HZH6661314/LC-Power-Supply/code/LC_Power/Docs/嵌入式架构设计培训计划（基于100W数字电源项目）.md

# 嵌入式架构设计培训计划（基于100W数字电源项目）

## 培训背景

**学员水平：** 初级（1-2年经验）
**培训目标：** 掌握工程级别的嵌入式架构设计能力
**培训方式：** 理论与实战结合
**实战项目：** 100W数控便携可调直流电源（STM32F334 + Buck-Boost）

------

## 项目架构概览

根据《数控电源代码规范.md》，项目采用**六层架构**：

```
┌─────────────────────────────────────────────────────┐
│  0_SysCore (Scheduler层)                            │
│  - SysTick时间片轮询                                │
│  - 全局中断配置                                      │
│  - 临界区并发保护                                    │
└─────────────────────────────────────────────────────┘
                        ↓ 可调用下方各层
┌─────────────────────────────────────────────────────┐
│  1_Product层                                        │
│  - UI显示、上位机协议、参数存储调度                  │
└─────────────────────────────────────────────────────┘
                        ↓
┌─────────────────────────────────────────────────────┐
│  2_Application层                                    │
│  - 状态机(BOOT/STANDBY/SOFTSTART/RUNNING/FAULT)    │
│  - 保护逻辑、PD诱骗握手                             │
└─────────────────────────────────────────────────────┘
                        ↓
┌─────────────────────────────────────────────────────┐
│  3_Control层 【纯C数学运算，严禁依赖底层】           │
│  - 电压环PID、电流环2P2Z、软件滤波器                 │
└─────────────────────────────────────────────────────┘
                        ↓
┌─────────────────────────────────────────────────────┐
│  4_Driver层                                         │
│  - W25Q256驱动、OLED驱动、INA240参数换算            │
└─────────────────────────────────────────────────────┘
                        ↓
┌─────────────────────────────────────────────────────┐
│  5_BSP层                                            │
│  - STM32F334 HAL库、HRTIM、ADC/DMA、SPI底层收发     │
└─────────────────────────────────────────────────────┘
```

------

## 第一阶段：架构设计三大铁律（2周，理论为主）

### 模块1：铁律一 - 严格的单向依赖与隔离

**核心原则：**

1. **上层可以调用下层，下层绝对不能知道上层的存在**
2. **同层之间禁止直接通信，必须通过全局Context**

**理论讲解：**

**为什么需要单向依赖？**

- 防止循环依赖（A调B，B调A，代码改不动）
- 保证可移植性（底层换芯片，上层不受影响）
- 降低耦合度（修改一个模块不影响其他模块）

**正确示例：**

```c
// ✅ 允许：Product层读取Control层数据
void UI_Display_Voltage(void) {
    int32_t voltage = g_sys_context.real_voltage_mv;
    TFT_DrawNumber(voltage);
}
```

**错误示例：**

```c
// ❌ 严禁：Driver层ADC中断直接调用Application层
void ADC_IRQHandler(void) {
    uint32_t adc_value = ADC1->DR;
    App_State_SwitchTo(STATE_FAULT);  // 错误！底层不能调上层
}
```

**正确做法：**

```c
// ✅ ADC中断只处理数据
void ADC_IRQHandler(void) {
    g_sys_context.adc_raw_value = ADC1->DR;
}

// Application层在1ms任务中检查
void Task_1ms(void) {
    if (g_sys_context.adc_raw_value > OVP_THRESHOLD) {
        App_State_SwitchTo(STATE_FAULT);
    }
}
```

**同层通信规则：**

```c
// ❌ 错误：protection.c直接调用ui.c
void Protection_Check(void) {
    if (over_voltage) {
        UI_ShowFaultDialog();  // 错误！同层直接调用
    }
}

// ✅ 正确：通过全局Context通信
void Protection_Check(void) {
    if (over_voltage) {
        g_sys_context.fault_code = FAULT_OVP;
    }
}

void UI_Task_50ms(void) {
    if (g_sys_context.fault_code != FAULT_NONE) {
        UI_ShowFaultDialog();
    }
}
```

**实战练习：**

1. 绘制你项目的依赖关系图
2. 检查代码中是否有违反单向依赖的地方
3. 设计全局Context结构体（PowerSystemContext_t）
4. 重构一个模块，消除跨层调用

------

### 模块2：铁律二 - 平台移植测试（试金石）

**核心原则：** 假设明天STM32F334缺货，必须换用TI C2000 DSP。

- **合格线：** 只需要删掉并重写`4_Driver`和`5_BSP`文件夹
- **黄金标准：** `3_Control`文件夹内的`pid_voltage.c`**绝对不允许有哪怕一行代码的修改**

**理论讲解：**

**Control层的纯净性要求：**

```c
// ✅ 正确：Control层只有纯C数学运算
float PID_Calculate(float target, float current) {
    float error = target - current;
    float output = Kp * error + Ki * integral + Kd * derivative;
    return output;
}

// ❌ 错误：Control层出现硬件相关代码
float PID_Calculate(float target, float current) {
    float error = target - current;
    HAL_GPIO_WritePin(LED_GPIO_Port, LED_Pin, GPIO_PIN_SET);  // 错误！
    return Kp * error;
}

// ❌ 错误：Control层包含硬件头文件
#include "stm32f3xx_hal.h"  // 错误！严禁包含底层头文件
```

**正确的数据流动：**

```c
// Scheduler层协调数据流动
void Task_1ms(void) {
    // 1. 从底层读取数据
    float voltage = BSP_ADC_GetVoltage();
    
    // 2. 传入Control层计算
    float duty = PID_Voltage_Calculate(g_target_voltage, voltage);
    
    // 3. 下发给底层执行
    BSP_HRTIM_SetDuty(duty);
}
```

**实战练习：**

1. 检查Control层代码，是否包含任何硬件相关头文件
2. 尝试在PC上编译Control层代码（使用gcc）
3. 思考：如果要移植到Arduino，哪些文件需要重写？
4. 编写一个移植指南文档

------

### 模块3：铁律三 - 数据的跨层传递（消灭extern）

**核心原则：** 使用"函数参数与返回值"进行依赖注入，严禁使用extern导致全局变量漫天飞。

**理论讲解：**

**错误示例：extern满天飞**

```c
// pid_voltage.c (Control层)
extern uint32_t g_adc_voltage;  // 错误！
extern void HRTIM_SetDuty(uint16_t duty);  // 错误！

float PID_Calculate(void) {
    float voltage = g_adc_voltage * 0.001f;
    float duty = Kp * (target - voltage);
    HRTIM_SetDuty((uint16_t)duty);
    return duty;
}
```

**正确示例：依赖注入**

```c
// pid_voltage.c (Control层) - 纯函数
float PID_Calculate(float target, float current) {
    float error = target - current;
    s_integral += error * dt;
    float derivative = (error - s_last_error) / dt;
    s_last_error = error;
    
    return Kp * error + Ki * s_integral + Kd * derivative;
}

// task_manager.c (Scheduler层)
void Task_1ms(void) {
    float voltage = BSP_ADC_GetVoltage() / 1000.0f;
    float duty = PID_Calculate(g_target_voltage, voltage);
    
    // 限幅
    if (duty > 0.95f) duty = 0.95f;
    if (duty < 0.05f) duty = 0.05f;
    
    BSP_HRTIM_SetDuty((uint16_t)(duty * 1000));
}
```

**全局Context的正确使用：**

```c
// state_machine.h
typedef struct {
    int32_t  target_voltage_mv;
    int32_t  target_current_ma;
    int32_t  real_voltage_mv;
    int32_t  real_current_ma;
    SystemState_t state;
    FaultCode_t   fault_code;
    uint16_t pwm_duty;
} PowerSystemContext_t;

extern PowerSystemContext_t g_sys_context;  // 唯一允许的全局变量
```

**实战练习：**

1. 设计PowerSystemContext_t结构体
2. 重构一个函数，消除extern，改用依赖注入
3. 统计项目中有多少个extern变量，制定消除计划

------

## 第二阶段：时间域管理与状态机（3周，理论+实战）

### 模块4：时间域管理（Task Scheduling）

**核心概念：** 系统任务按紧急程度划分为三个域，严禁跨域干扰：

1. **极速域 (Isr_Critical):** HRTIM/ADC中断
   - 仅处理环路计算、更新PWM占空比、紧急限流
   - 耗时须 < 1.5us
2. **实时域 (Task_1ms):** SysTick触发
   - 执行状态机、软件保护检查、PID目标值平滑增减
3. **异步域 (Task_Main):** 主循环轮询
   - 执行屏幕刷新、Flash写入、串口调试

**理论讲解：**

**为什么要划分时间域？**

- 保证实时性（紧急任务不被慢速任务阻塞）
- 降低CPU占用率（不同优先级任务分时执行）
- 避免任务冲突（快速任务和慢速任务隔离）

**时间域划分原则：**

```c
// 极速域：中断内处理（< 1.5us）
void ADC_IRQHandler(void) {
    uint32_t adc_value = ADC1->DR;
    
    // 硬保护：立即停止PWM
    if (adc_value > CRITICAL_THRESHOLD) {
        Drv_Hrtim_EmergencyStop();
    }
}

// 实时域：1ms任务
void Task_1ms(void) {
    StateMachine_Process();
    Protection_SoftCheck();
    PID_Control();
}

// 异步域：主循环
void Task_Main(void) {
    UI_Refresh();
    Flash_Write();
    UART_Process();
}
```

**实战练习：**

1. 分析你的项目，哪些任务属于哪个时间域？
2. 测量每个任务的执行时间（使用DWT）
3. 优化任务调度，降低CPU占用率
4. 实现任务执行时间监控和告警

------

### 模块5：状态机设计

**核心概念：** 状态机是嵌入式系统的核心，定义了系统的行为模式。

**五态状态机：**

```
STATE_BOOT (上电初始化)
    ↓ PD握手完成
STATE_STANDBY (待机，输出OFF)
    ↓ 用户按下输出按钮
STATE_SOFT_START (软启动)
    ↓ 占空比平滑拉升完成
STATE_RUNNING (运行，输出ON)
    ↓ 触发保护
STATE_FAULT (故障锁定)
    ↓ 用户手动复位
STATE_STANDBY
```

**理论讲解：**

**状态机的实现方式：**

```c
// 方式1：Switch-Case（简单但不优雅）
void StateMachine_Process(void) {
    switch (current_state) {
        case STATE_STANDBY:
            // 处理待机逻辑
            break;
        case STATE_RUNNING:
            // 处理运行逻辑
            break;
    }
}

// 方式2：函数指针表（推荐）
typedef struct {
    void (*Enter)(void);
    void (*Run)(void);
    void (*Exit)(void);
} StateHandler_t;

StateHandler_t g_state_handlers[] = {
    [STATE_STANDBY] = { Standby_Enter, Standby_Run, Standby_Exit },
    [STATE_RUNNING] = { Running_Enter, Running_Run, Running_Exit },
};

void StateMachine_SwitchTo(SystemState_t new_state) {
    if (g_state_handlers[current_state].Exit) {
        g_state_handlers[current_state].Exit();
    }
    
    current_state = new_state;
    
    if (g_state_handlers[current_state].Enter) {
        g_state_handlers[current_state].Enter();
    }
}
```

**实战练习：**

1. 绘制完整的状态转移图
2. 实现五个状态的Enter/Run/Exit函数
3. 实现STATE_SOFT_START的占空比平滑拉升算法
4. 添加状态转移日志，便于调试

------

## 第三阶段：控制算法与保护机制（4周，实战为主）

### 模块6：电压环PID控制

**理论知识：** PID控制是最常用的闭环控制算法，由比例(P)、积分(I)、微分(D)三部分组成。

**PID公式：**

```
output = Kp * error + Ki * ∫error*dt + Kd * d(error)/dt
```

**实战练习：**

1. 实现基础PID算法
2. 添加积分限幅（防止积分饱和）
3. 添加微分滤波（降低噪声影响）
4. 参数整定（Ziegler-Nichols方法）
5. 单元测试（Python生成测试数据）

**代码实现：**

```c
// pid_voltage.c
typedef struct {
    float Kp;
    float Ki;
    float Kd;
    float integral;
    float last_error;
    float integral_max;
} PID_t;

float PID_Calculate(PID_t *pid, float target, float current) {
    float error = target - current;
    
    // 积分项
    pid->integral += error * DT;
    if (pid->integral > pid->integral_max) {
        pid->integral = pid->integral_max;
    }
    if (pid->integral < -pid->integral_max) {
        pid->integral = -pid->integral_max;
    }
    
    // 微分项
    float derivative = (error - pid->last_error) / DT;
    pid->last_error = error;
    
    // 输出
    return pid->Kp * error + pid->Ki * pid->integral + pid->Kd * derivative;
}
```

------

### 模块7：电流环2P2Z控制

**理论知识：** 2P2Z（2极2零点）补偿器是数字电源中常用的控制算法，比PID更适合高频控制。

**差分方程：**

```
y[n] = b0*x[n] + b1*x[n-1] + b2*x[n-2] - a1*y[n-1] - a2*y[n-2]
```

**实战练习：**

1. 理解2P2Z补偿原理
2. 实现差分方程
3. 参数设计（根据Buck-Boost传递函数）
4. 与PID对比测试

------

### 模块8：保护机制设计

**核心概念：** 保护机制分为硬保护和软保护。

**硬保护（中断内处理）：**

```c
void ADC_IRQHandler(void) {
    uint32_t current = ADC_GetCurrent();
    
    // 短路保护：立即停止PWM
    if (current > SCP_THRESHOLD) {
        Drv_Hrtim_EmergencyStop();
        g_sys_context.fault_code = FAULT_SCP;
    }
}
```

**软保护（主循环处理）：**

```c
void Protection_Process(void) {
    // 过热保护：逐步降功率
    if (g_sys_context.temperature > OTP_THRESHOLD) {
        g_sys_context.pwm_duty *= 0.9f;
    }
}
```

**实战练习：**

1. 实现六大保护功能（OVP、OCP、SCP、OTP、OPP、反接）
2. 设计保护优先级
3. 实现故障记录和上报
4. 添加保护自检功能

------

## 第四阶段：架构优化与重构（3周，实战为主）

### 模块9：当前项目架构诊断

**问题1：缺少错误处理机制**

**优化方案：统一错误码设计**

```c
typedef enum {
    ERR_OK = 0,
    ERR_PARAM_INVALID,
    ERR_TIMEOUT,
    ERR_HARDWARE_FAULT,
} ErrorCode_t;

ErrorCode_t BSP_ADC_Read(uint32_t *value);
```

**问题2：缺少单元测试**

**优化方案：搭建测试框架**

```c
void test_PID_Voltage(void) {
    PID_Init(1.0, 0.1, 0.01);
    float output = PID_Calculate(10.0, 0.0);
    TEST_ASSERT_FLOAT_WITHIN(0.1, 10.0, output);
}
```

**实战练习：**

1. 为所有关键函数添加返回值
2. 实现错误日志记录
3. 搭建Unity测试框架
4. 为Control层编写单元测试

------

### 模块10：性能优化

**优化技术：**

1. 查表法（三角函数、开方）
2. 定点数运算（替代浮点数）
3. DMA传输（ADC、SPI）
4. 局部刷新（TFT）

**实战练习：**

1. 使用DWT测量函数执行时间
2. 优化PID计算（定点数）
3. 优化ADC采样（DMA模式）
4. 优化TFT刷新（局部刷新）

------

## 第五阶段：文档与总结（1周）

### 模块11：架构文档编写

**文档内容：**

1. 架构全景图
2. 分层说明
3. 模块职责
4. 接口定义
5. 数据流图
6. 状态转移图

**实战练习：**

1. 编写项目架构设计文档
2. 绘制UML类图、时序图
3. 编写接口说明文档
4. 编写移植指南

------

## 培训时间安排

| 阶段 | 内容 | 时间 | 形式 |
| :--- | :--- | :--- | :--- |
| 第一阶段 | 三大铁律 | 2周 | 理论讲解 + 代码分析 |
| 第二阶段 | 时间域与状态机 | 3周 | 理论 + 实战 |
| 第三阶段 | 控制算法与保护 | 4周 | 实战为主 |
| 第四阶段 | 优化与重构 | 3周 | 实战为主 |
| 第五阶段 | 文档与总结 | 1周 | 文档编写 |
| **总计** | **11个模块** | **13周** | **约3个月** |

------

## 学习成果验收

完成培训后，你应该能够：

1. **理论能力：**
   - 深刻理解三大架构铁律
   - 掌握时间域管理和状态机设计
   - 了解嵌入式系统的特殊性
2. **实战能力：**
   - 独立设计中等规模嵌入式项目的架构
   - 能够重构现有代码，提高可维护性
   - 能够编写清晰的架构文档
3. **项目成果：**
   - 完成100W数字电源的完整实现
   - 代码结构清晰，分层合理
   - 具备良好的可移植性

------

## 关键文件清单

| 模块 | 关键文件 |
| :--- | :--- |
| 状态机 | `/Layer/Application/state_machine.c` |
| 控制算法 | `/Layer/Control/pid_voltage.c`, `/Layer/Control/2p2z_current.c` |
| 保护机制 | `/Layer/Application/protection.c` |
| 任务调度 | `/Layer/Scheduler/task_manager.c` |
| 按键处理 | `/Layer/Product/key.c` |
| BSP抽象  | `/Layer/Bsp/bsp_hrtim.c`, `/Layer/Bsp/bsp_adc.c` |

------

## 培训重点强调

1. **三大铁律是架构的基石，必须严格遵守**
2. **Control层的纯净性是可移植性的关键**
3. **时间域管理是实时性的保证**
4. **状态机是系统行为的核心**
5. **保护机制是安全性的基础**
