HZH6661314/LC-Power-Supply/code/LC_Power/Layer/Driver/tft_selftest.h

#ifndef TFT_SELFTEST_H
#define TFT_SELFTEST_H

#ifdef __cplusplus
extern "C" {
#endif

#include "tft_gfx.h"

void TFT_SelfTest_DrawMappingPage(void);

#ifdef __cplusplus
}
#endif

#endif /* TFT_SELFTEST_H */
